wireless-tag-com/WT9932Cx-TINY/other/WT9932C2-TINY/WT9932C2-TINY.png

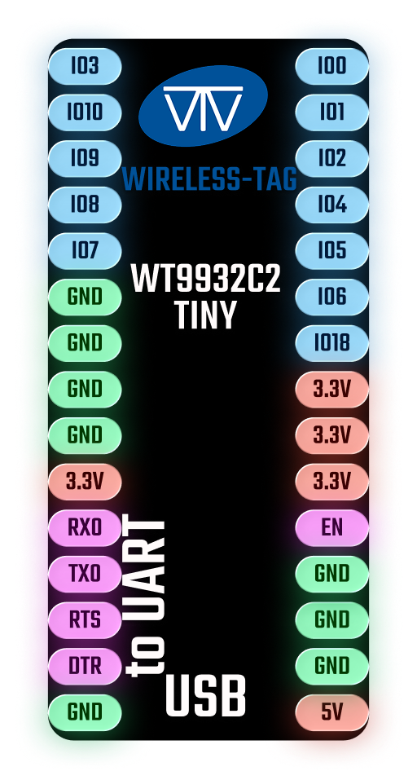
other/WT9932C2-TINY/WT9932C2-TINY.png
